ucsbieee/mapache64/fpga/dv/gpu/gold_images/obs_stress.png

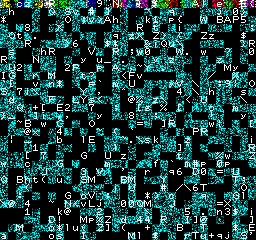
fpga/dv/gpu/gold_images/obs_stress.png
