ucsbieee/mapache64/fpga/dv/gpu/gold_images/random_yellow_white.png

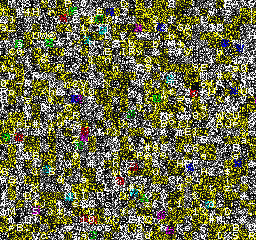
fpga/dv/gpu/gold_images/random_yellow_white.png
