ucsbieee/mapache64/hardware-level/src/gpu-max_parallel/top.tb.v

`include "modules/gpu.v"

`include "parameters.v"

module top ();

reg clk_12_5875 = 1;
always #( `GPU_CLK_PERIOD / 2 ) clk_12_5875 = ~clk_12_5875;

reg rst;
wire [1:0] r, g, b;
wire hsync, vsync;
reg [7:0] data;
reg [`VRAM_ADDR_WIDTH-1:0] address;
reg cs;

gpu_m gpu (
    clk_12_5875, rst,
    r,g,b, hsync, vsync,
    data, address, cs
);

/* Test */
initial begin
$dumpfile( "dump.vcd" );
$dumpvars();
$timeformat( -3, 6, "ms", 0);
//\\ =========================== \\//

rst = 1;
#( `GPU_CLK_PERIOD / 2 )
rst = 0;

#( 0.02 )

//\\ =========================== \\//
$finish ;
end

endmodule
