ucsbieee/mapache64/fpga/synth/cmod_a7/clk_mmcm.v

module clk_mmcm(clk_12_5875, clk_5, reset, clk_in1)
/* synthesis syn_black_box black_box_pad_pin="clk_12_5875,clk_5,reset,clk_in1" */;
  output clk_12_5875;
  output clk_5;
  input reset;
  input clk_in1;
endmodule
