ucsbieee/mapache64/assembly-level/src/firmware/subroutines/misc_Q9_6.asm

; converts Q9_6_I1 to INT8_O
Q9_6_to_SINT8:
        pha

        ; push lsb of Q9_6_I1
        lda Q9_6_I1
        pha

        ; copy msb of Q9_6_I1 to out
        cp8 Q9_6_I1+1, INT8_O

        rol Q9_6_I1
        rol INT8_O
        rol Q9_6_I1
        rol INT8_O

        ; pull msb of Q9_6_I1
        pla
        sta Q9_6_I1

        pla
        rts



; converts Q9_6_I1 to INT16_O
Q9_6_to_SINT16:
        pha


        ; MSB
        bit Q9_6_I1+1

        ; sign extend
        bmi .negative
.positive:
        lda #%00000000
        bra .sign_done
.negative:
        lda #%11111110
.sign_done:
        sta INT16_O+1

        ; add 1 if 6th bit is set
        lda #%01000000
        bit Q9_6_I1+1
        beq .last_bit_handled
        inc INT16_O+1
.last_bit_handled:

        ; LSB

        ; push lsb of Q9_6_I1
        lda Q9_6_I1
        pha

        cp8 Q9_6_I1+1, INT16_O

        rol Q9_6_I1
        rol INT16_O
        rol Q9_6_I1
        rol INT16_O

        ; pull msb of Q9_6_I1
        pla
        sta Q9_6_I1

        pla
        rts


; The minimum of Q9_6_I1 and Q9_6_I2 is copied to Q9_6_O
Q9_6_min:
        pha

        ; TO DO

        pla
        rts


; The maximum of Q9_6_I1 and Q9_6_I2 is copied to Q9_6_O
Q9_6_max:
        pha

        ; TO DO

        pla
        rts
