ucsbieee/mapache64/firmware/demos/game/main.c

// ==================== game.c ==================== //
// Follow this file template to implement your game //
// ================================================ //

#define SIM 1 // change value depending if running simulation or not


// ================================ //

#pragma code-name ("CODE")
#pragma bss-name ("BSS")

#include <int.h>
#include <vram.h>
#include <stop.h>
#include <Q9_6.h>
#include <mapache64_zero_page.h>
#include <controller.h>

// ================================ //


uint16_t CONTROLLER_1_PEDGE;
uint16_t CONTROLLER_1_PREV;

bool vram_initialized;


#include "patterns.h"
#include "person.h"

person_t p;






void reset(void) {
    CONTROLLER_1_PREV = 0;

    p.xp=SINT_TO_Q9_6(124);
    p.yp=ground;
    p.xv=0;
    p.yv=0;
    p.object=0;
    p.pmfa=person_normal_pmfa;
    p.color=YELLOW_C_MASK;

    vram_initialized = false;
}






void do_logic(void) {
    // calculate positive edge of all controller buttons
    CONTROLLER_1_PEDGE = (~CONTROLLER_1_PREV)&CONTROLLER_1;
    CONTROLLER_1_PREV = CONTROLLER_1;

    // check for reset button
    if ( CONTROLLER_1_PEDGE & CONTROLLER_START_MASK )
        reset();

    // check for jump button
    if ( CONTROLLER_1_PEDGE & CONTROLLER_A_MASK )
        person_jump(&p);

    // check for left or right
    if ( CONTROLLER_1 & CONTROLLER_LEFT_MASK )
        p.xv -= person_horizontal_acc;
    if ( CONTROLLER_1 & CONTROLLER_RIGHT_MASK )
        p.xv += person_horizontal_acc;

    // update person postion
    person_advance(&p);
}






void init_vram(void);

void fill_vram(void) {
    if (!vram_initialized) init_vram();
    person_draw(&p);
}


void init_vram(void) {
    uint8_t i, j;

    // clear vram
    for (i = 0; i < 64; i++) {
        OBM[i].y = 0xff;
    }

    // load background patterns
    load_background_pattern(black,black_pmba);
    load_background_pattern(dark_gray,dark_gray_pmba);
    load_background_pattern(light_gray,light_gray_pmba);
    load_background_pattern(white,white_pmba);

    // load foreground patterns
    load_foreground_pattern(person_normal,person_normal_pmfa);

    // load background
    background_palette = CYAN_C0_MASK | GREEN_C1_MASK;
    for (i = 0; i < 28; i++) {
        for (j = 0; j < 32; j++) {
            NTBL[i][j] = white_pmba;
        }
    }
    for (i = 28; i < 30; i++) {
        for (j = 0; j < 32; j++) {
            NTBL[i][j] = light_gray_pmba | COLOR_SELECT_MASK;
        }
    }

    vram_initialized = true;
}
